mikeneiderhauser/CRSFJoystick/photos/HGLRC_CRSFJoystick/board_render_front_V1.1.jpg

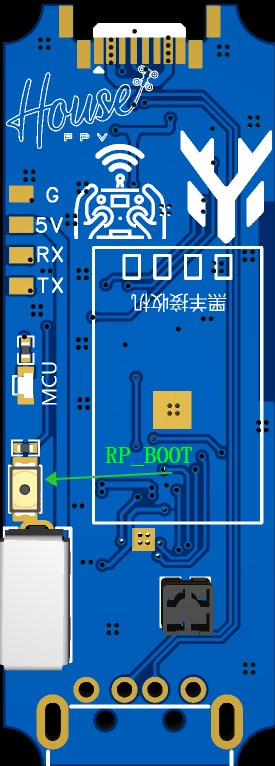
photos/HGLRC_CRSFJoystick/board_render_front_V1.1.jpg
