mikeneiderhauser/CRSFJoystick/photos/HGLRC_CRSFJoystick/board_v1.0_back.png

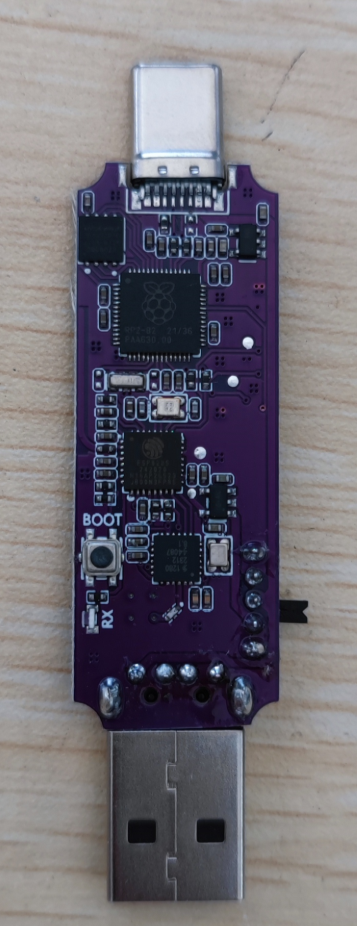
photos/HGLRC_CRSFJoystick/board_v1.0_back.png
