mikeneiderhauser/CRSFJoystick/photos/HGLRC_CRSFJoystick/board_v1.0_front.png

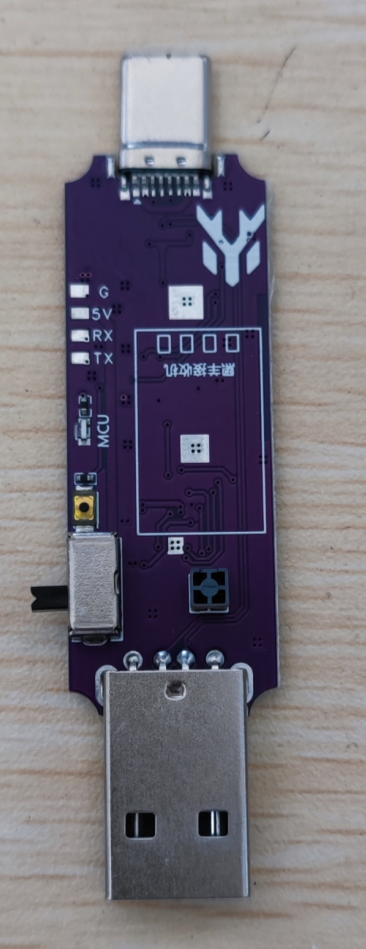
photos/HGLRC_CRSFJoystick/board_v1.0_front.png
