mikeneiderhauser/CRSFJoystick/photos/pico/board_render_back.png

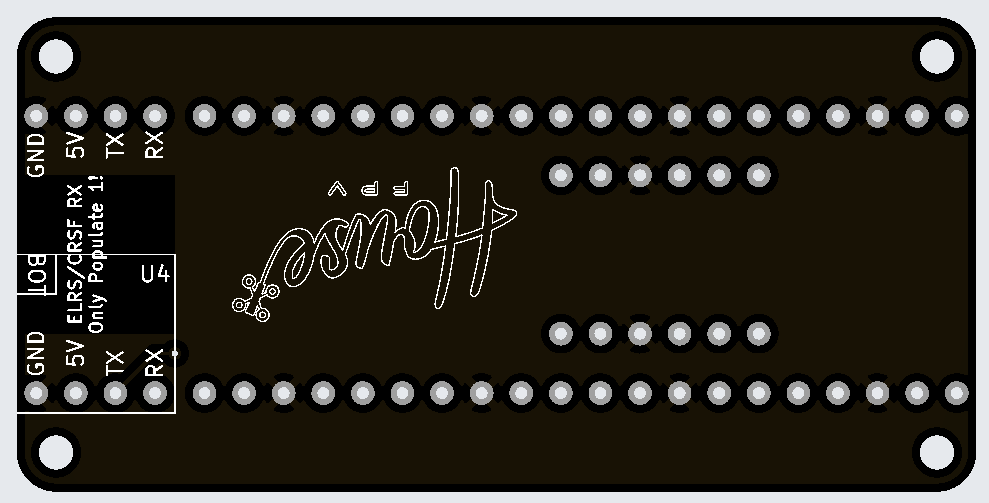
photos/pico/board_render_back.png
