mikeneiderhauser/CRSFJoystick/photos/pico/Pico_level_shifter.jpg

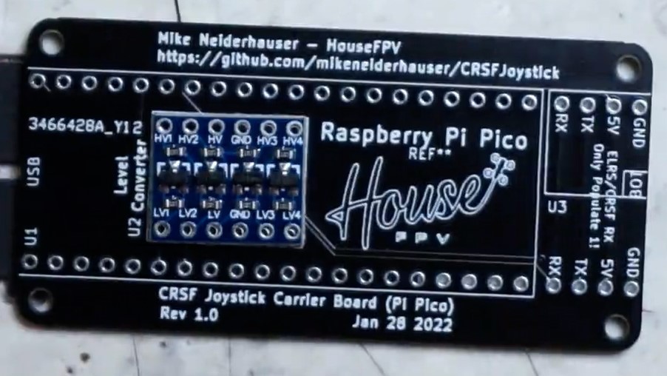
photos/pico/Pico_level_shifter.jpg
