mikeneiderhauser/CRSFJoystick/photos/tiny/2040_level_shifter.jpg

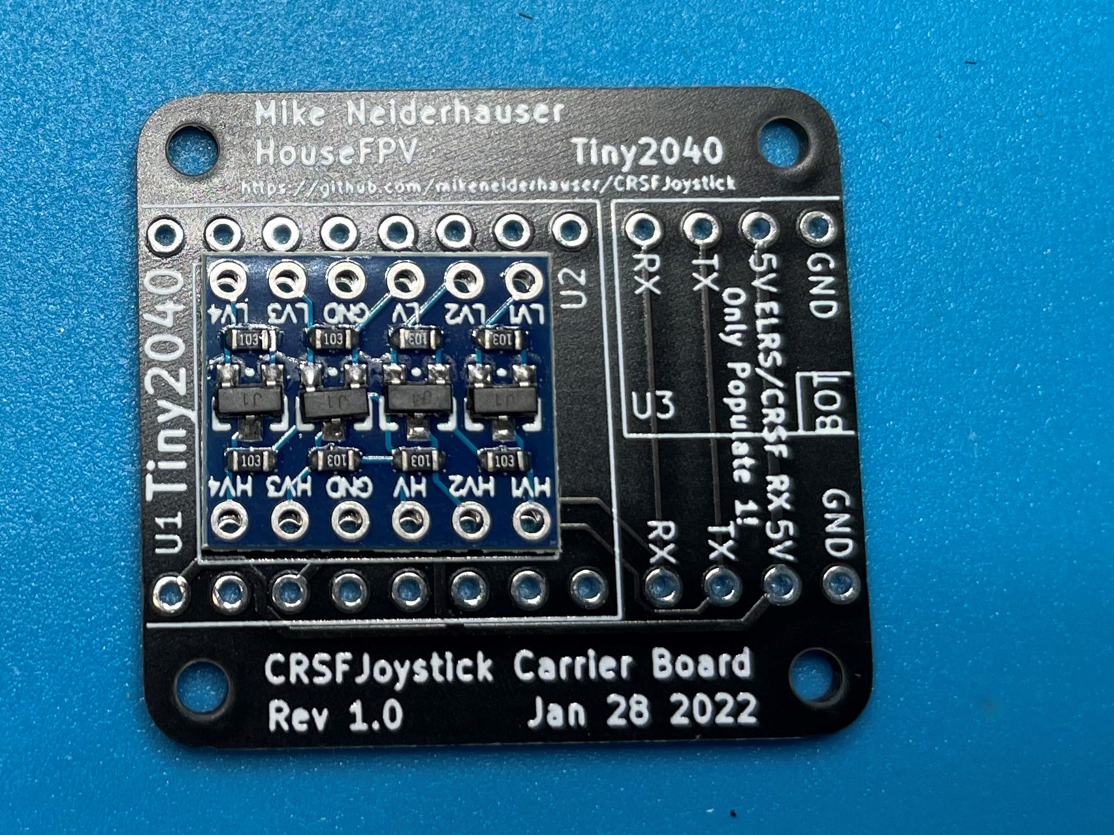
photos/tiny/2040_level_shifter.jpg
