mikeneiderhauser/CRSFJoystick/photos/tiny/board_render_back.png

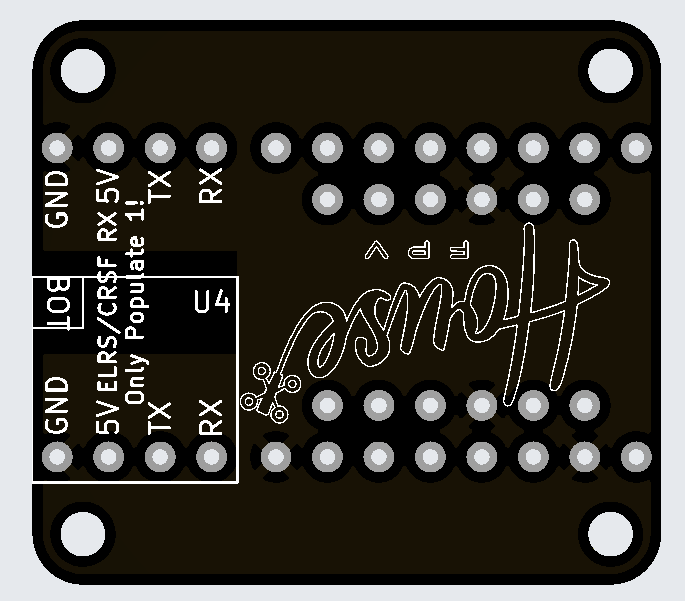
photos/tiny/board_render_back.png
