mikeneiderhauser/CRSFJoystick/photos/proto_breadboard2.jpg

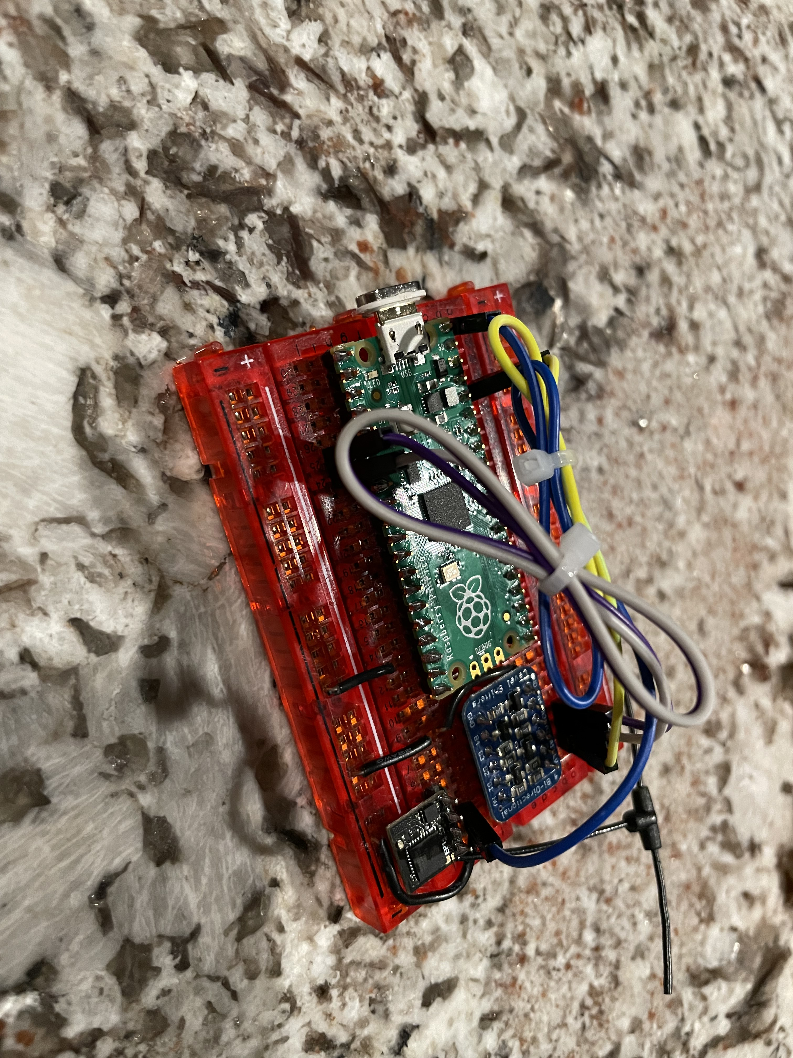
photos/proto_breadboard2.jpg
