mikeneiderhauser/CRSFJoystick/photos/proto_breadboard.jpg

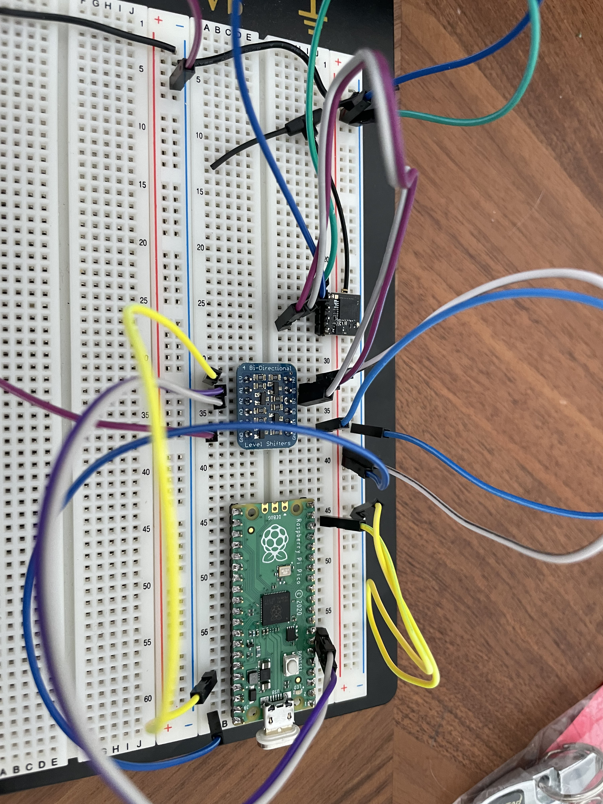
photos/proto_breadboard.jpg
